r4stl1n/micro-hal/parts/3d-prints/stl/templates/Rear_Cover (Template).stl

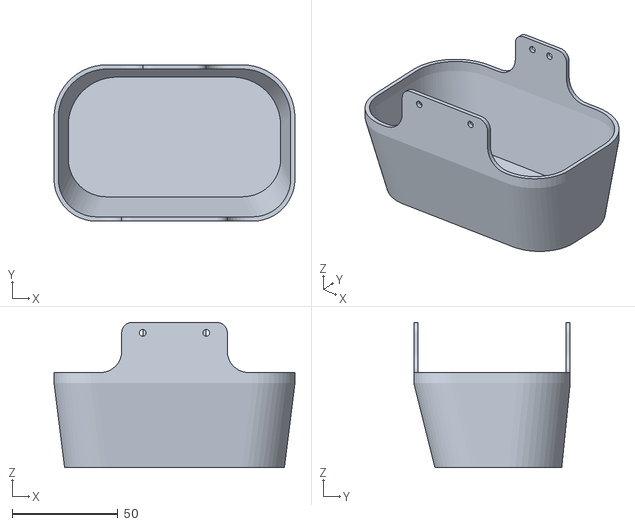
[picture p16: CAD file, 2022-02-13]
parts/3d-prints/stl/templates/Rear_Cover (Template).stl
114.0 x 74.0 x 68.8
