r4stl1n/micro-hal/sim/meshes/stl/ledholder.stl

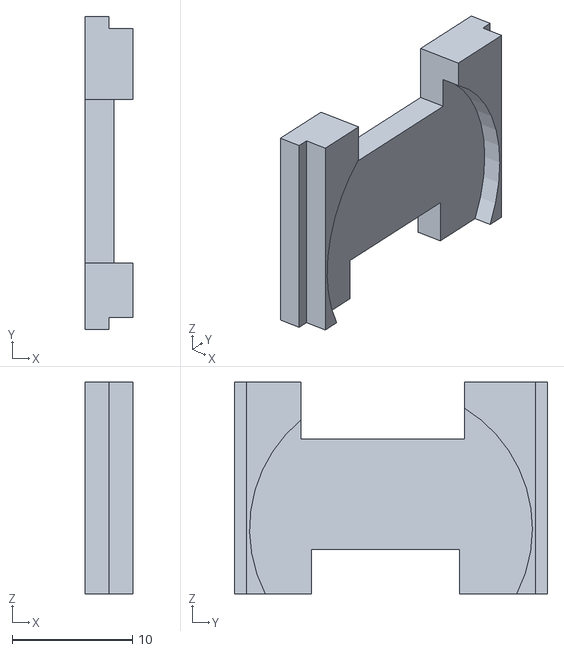
[picture p17: CAD file, 2022-02-22]
sim/meshes/stl/ledholder.stl
4.00 x 26.0 x 17.6
