r4stl1n/micro-hal/parts/3d-prints/freecad/LiPo_Mountingbracket_Front.FCStd

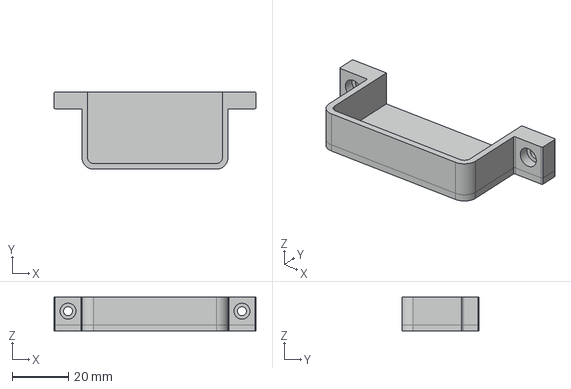
[picture p18: CAD file, 2022-02-13]
parts/3d-prints/freecad/LiPo_Mountingbracket_Front.FCStd
72.0 x 27.5 x 12.0 mm
