r4stl1n/micro-hal/sim/meshes/stl/lshoulder.stl

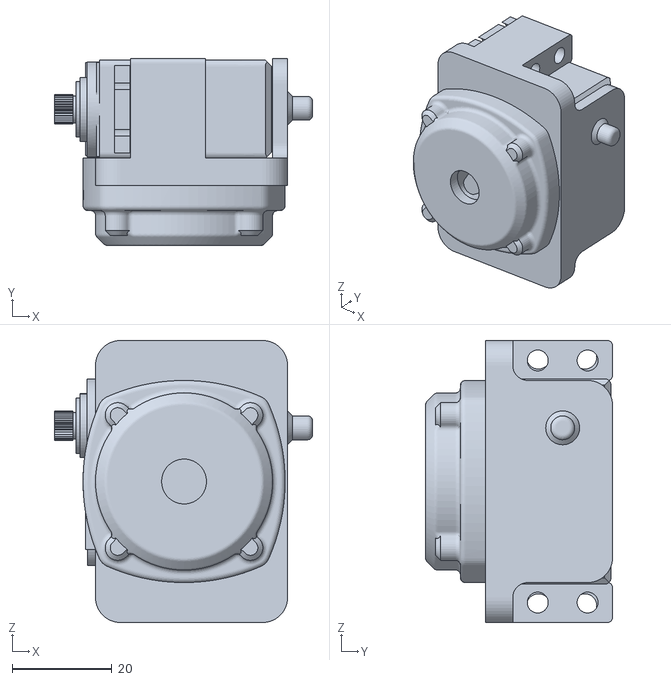
[picture p19: CAD file, 2022-02-22]
sim/meshes/stl/lshoulder.stl
51.7 x 37.5 x 56.5
