r4stl1n/micro-hal/parts/3d-prints/freecad/LiPo_Mountingbracket_Rear.FCStd

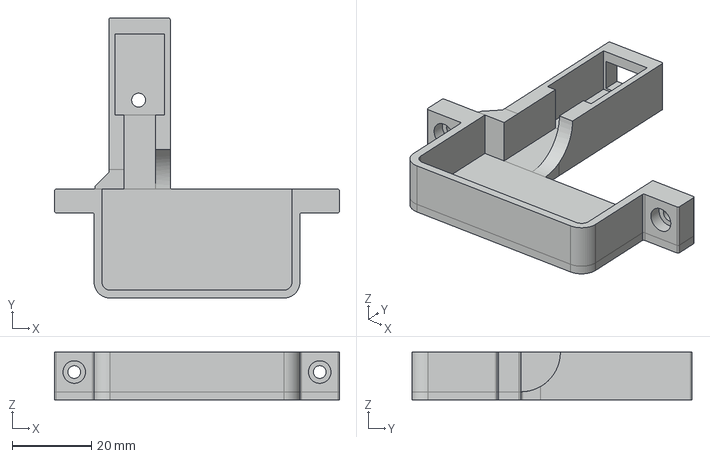
[picture p20: CAD file, 2022-02-13]
parts/3d-prints/freecad/LiPo_Mountingbracket_Rear.FCStd
72.0 x 70.8 x 12.0 mm
