r4stl1n/micro-hal/sim/meshes/stl/backpart.stl

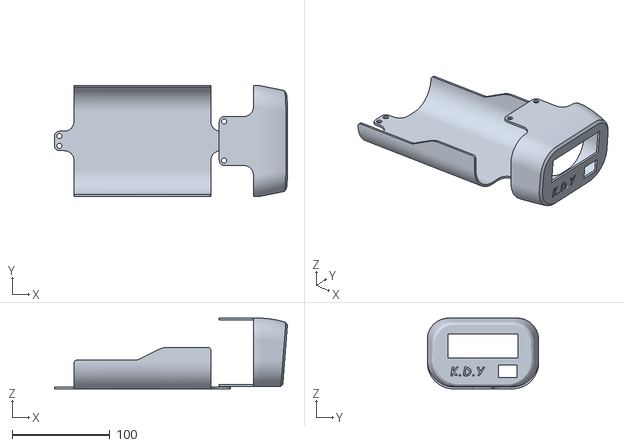
[picture p21: CAD file, 2022-02-22]
sim/meshes/stl/backpart.stl
238.4 x 114.1 x 72.5
