r4stl1n/micro-hal/sim/meshes/stl/F_shoulder.stl

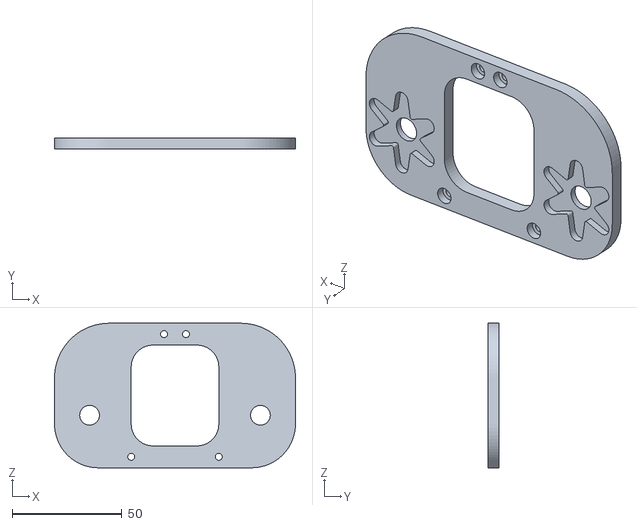
[picture p22: CAD file, 2022-02-22]
sim/meshes/stl/F_shoulder.stl
110.0 x 5.00 x 66.0
