r4stl1n/micro-hal/sim/meshes/stl/foot.stl

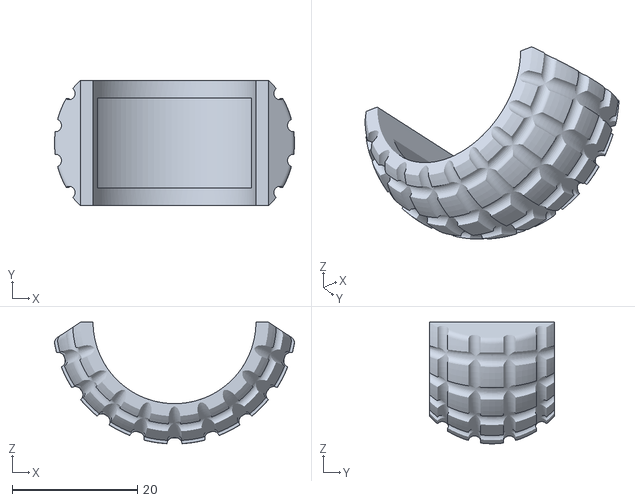
[picture p23: CAD file, 2022-02-22]
sim/meshes/stl/foot.stl
38.3 x 20.0 x 19.4
