r4stl1n/micro-hal/parts/3d-prints/freecad/Shoulder_Joint_Servohorn_Cap.FCStd

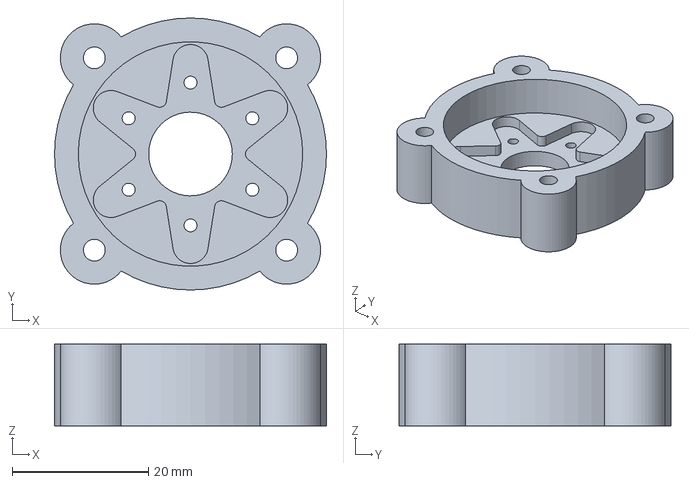
[picture p24: CAD file, 2022-02-13]
parts/3d-prints/freecad/Shoulder_Joint_Servohorn_Cap.FCStd
40.0 x 40.0 x 12.0 mm
