r4stl1n/micro-hal/sim/meshes/stl/non-mega_T_cover.stl

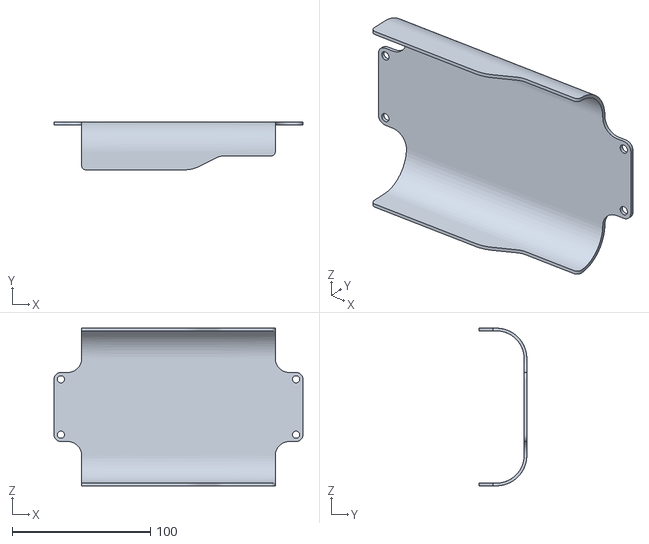
[picture p25: CAD file, 2022-02-22]
sim/meshes/stl/non-mega_T_cover.stl
180.0 x 34.5 x 114.0
