r4stl1n/micro-hal/sim/meshes/stl/batteryholder.stl

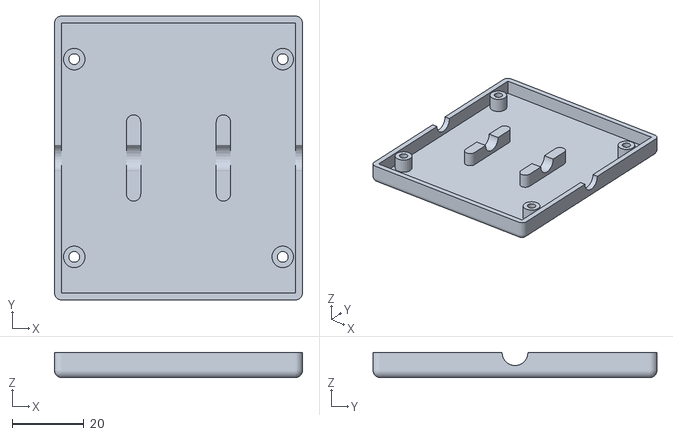
[picture p26: CAD file, 2022-02-22]
sim/meshes/stl/batteryholder.stl
69.0 x 79.0 x 7.00
