r4stl1n/micro-hal/parts/3d-prints/freecad/LiPo_Mountingbracket_Middle.FCStd

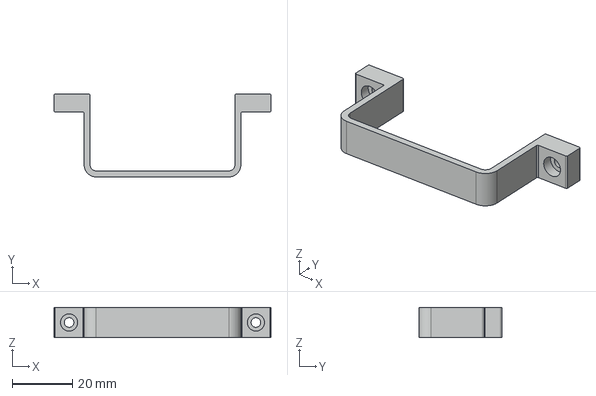
[picture p27: CAD file, 2022-02-13]
parts/3d-prints/freecad/LiPo_Mountingbracket_Middle.FCStd
72.0 x 27.5 x 10.0 mm
