r4stl1n/micro-hal/sim/meshes/stl/jetsonPlate.stl

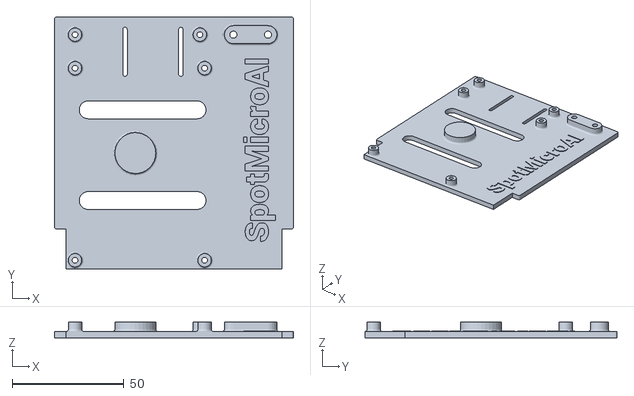
[picture p28: CAD file, 2022-02-22]
sim/meshes/stl/jetsonPlate.stl
107.0 x 113.0 x 7.10
