r4stl1n/micro-hal/parts/3d-prints/freecad/Limb_Top_Shell.FCStd

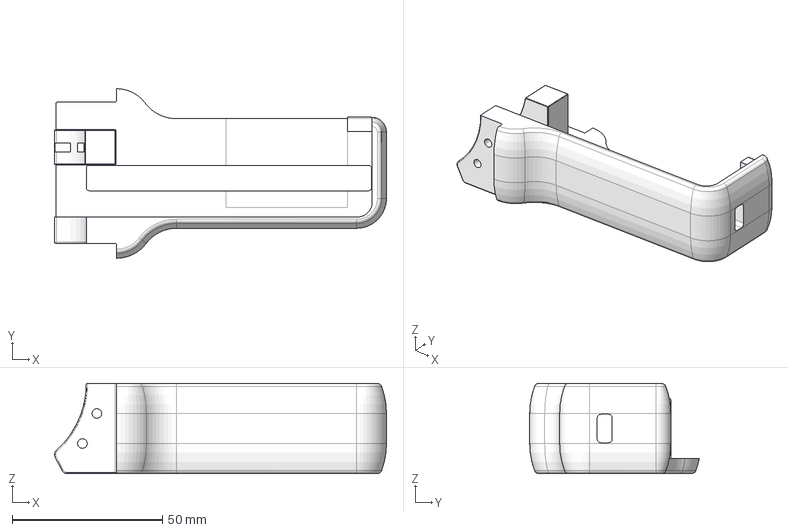
[picture p29: CAD file, 2022-02-13]
parts/3d-prints/freecad/Limb_Top_Shell.FCStd
110.6 x 56.5 x 30.0 mm
