r4stl1n/micro-hal/sim/meshes/stl/R_arm.stl

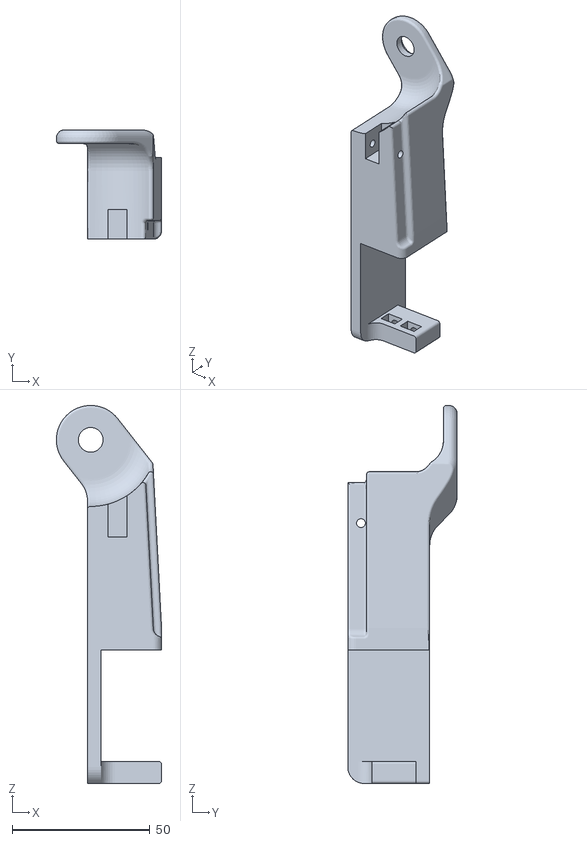
[picture p30: CAD file, 2022-02-22]
sim/meshes/stl/R_arm.stl
38.2 x 39.8 x 137.4
