r4stl1n/micro-hal/parts/3d-prints/freecad/Inner_Shoulder.FCStd

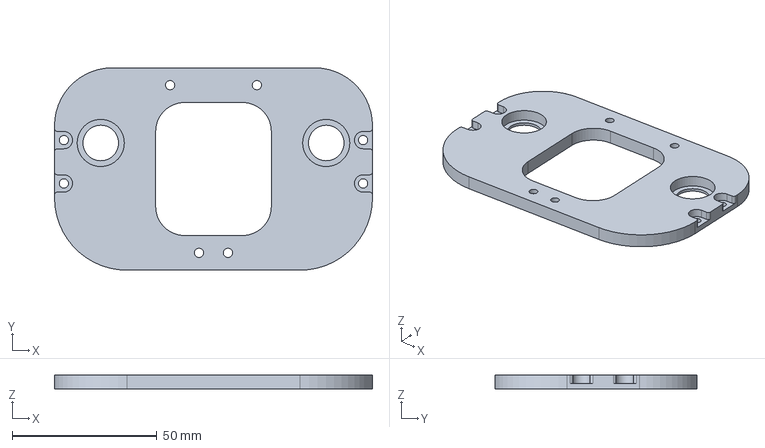
[picture p32: CAD file, 2022-02-13]
parts/3d-prints/freecad/Inner_Shoulder.FCStd
110.0 x 70.0 x 5.00 mm
