r4stl1n/micro-hal/sim/meshes/stl/R_side_plate.stl

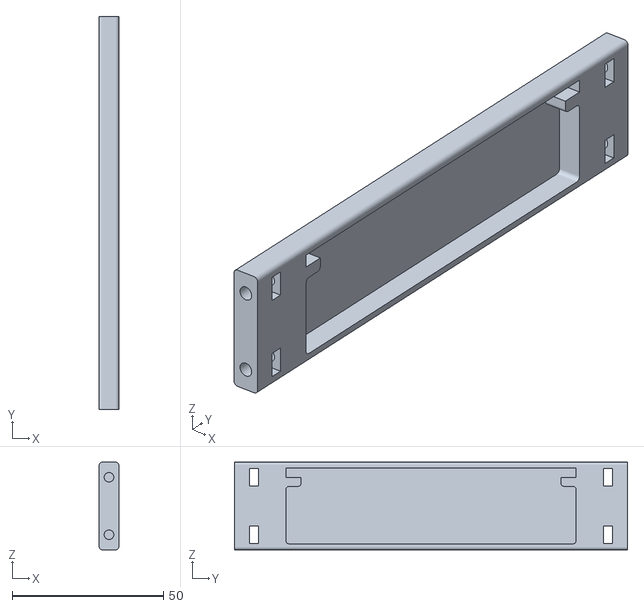
[picture p33: CAD file, 2022-02-22]
sim/meshes/stl/R_side_plate.stl
6.50 x 130.0 x 29.0
