r4stl1n/micro-hal/parts/3d-prints/freecad/Wrist.FCStd

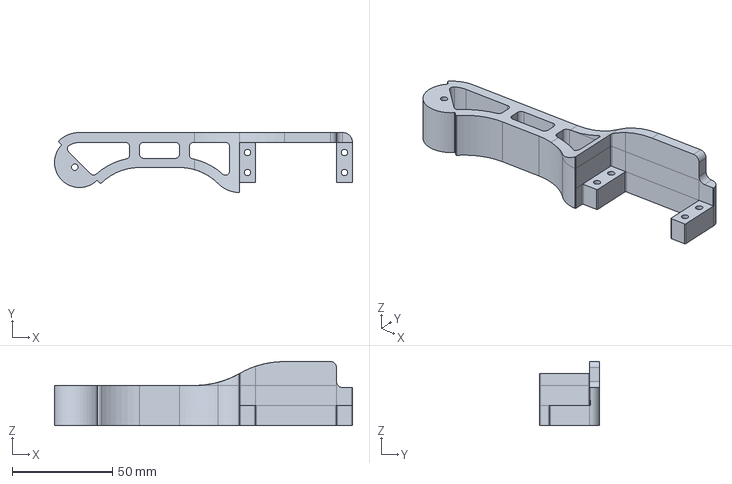
[picture p34: CAD file, 2022-02-13]
parts/3d-prints/freecad/Wrist.FCStd
149.0 x 30.0 x 32.0 mm
