r4stl1n/micro-hal/sim/meshes/stl/lfoot.stl

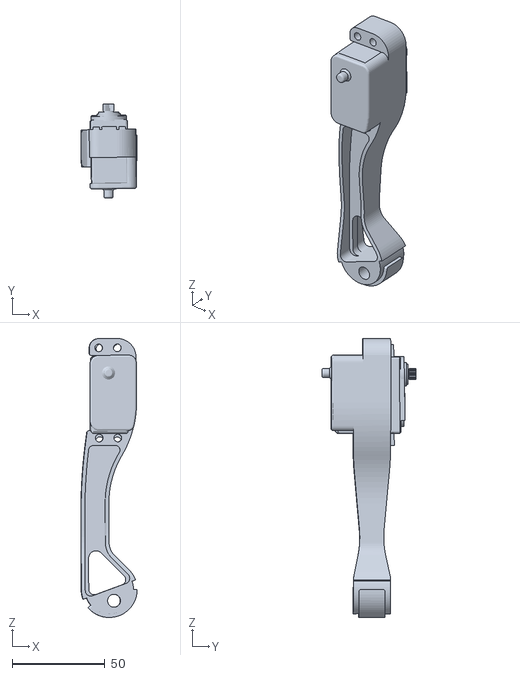
[picture p35: CAD file, 2022-02-22]
sim/meshes/stl/lfoot.stl
30.4 x 50.7 x 150.0
