r4stl1n/micro-hal/parts/3d-prints/freecad/Shoulder_Joint_Ball_Bearing_Pin.FCStd

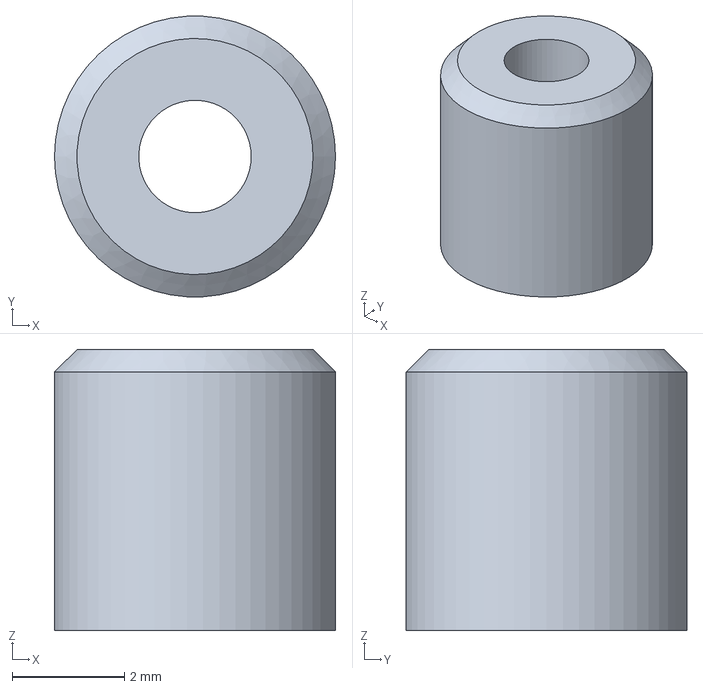
[picture p36: CAD file, 2022-02-13]
parts/3d-prints/freecad/Shoulder_Joint_Ball_Bearing_Pin.FCStd
5.00 x 4.99 x 5.00 mm
