r4stl1n/micro-hal/parts/3d-prints/freecad/Bottom_Cover_Split_Rear.FCStd

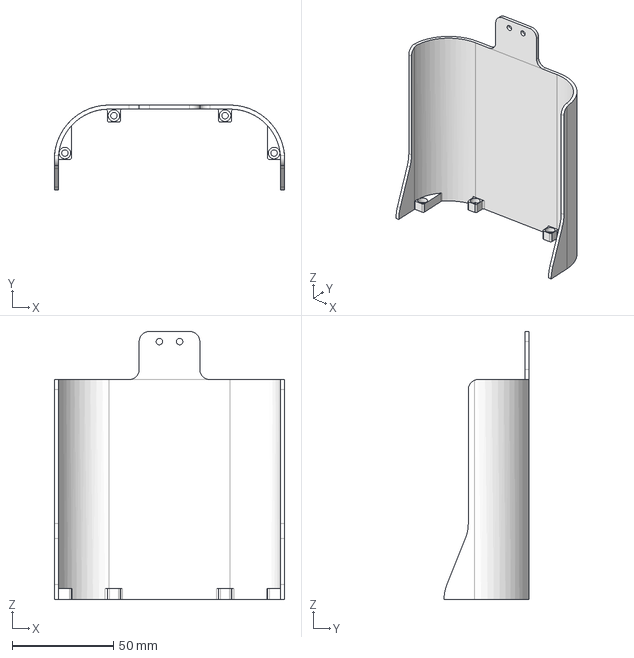
[picture p37: CAD file, 2022-02-13]
parts/3d-prints/freecad/Bottom_Cover_Split_Rear.FCStd
114.0 x 42.0 x 132.6 mm
