r4stl1n/micro-hal/sim/meshes/stl/rear.stl

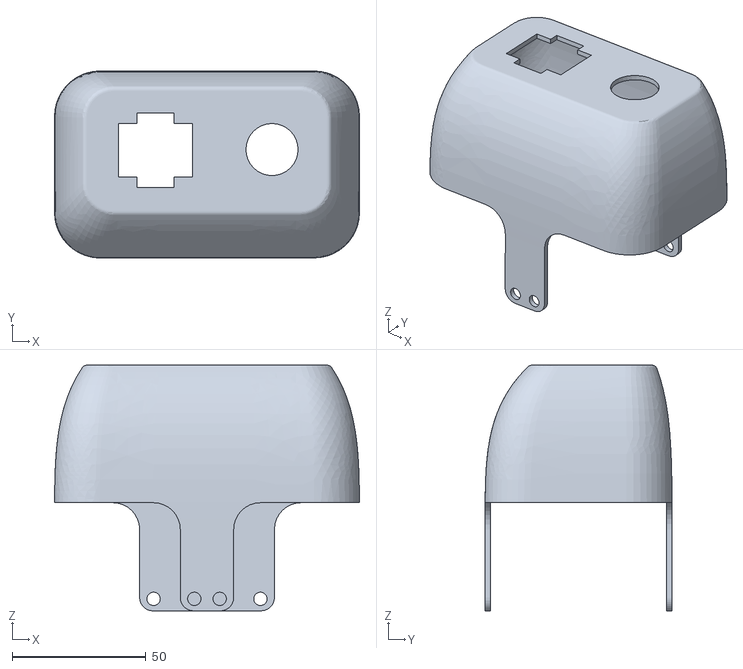
[picture p38: CAD file, 2022-02-22]
sim/meshes/stl/rear.stl
114.2 x 70.0 x 92.0
