r4stl1n/micro-hal/parts/3d-prints/freecad/Limb_Servohorn_Mount_long_v4.FCStd

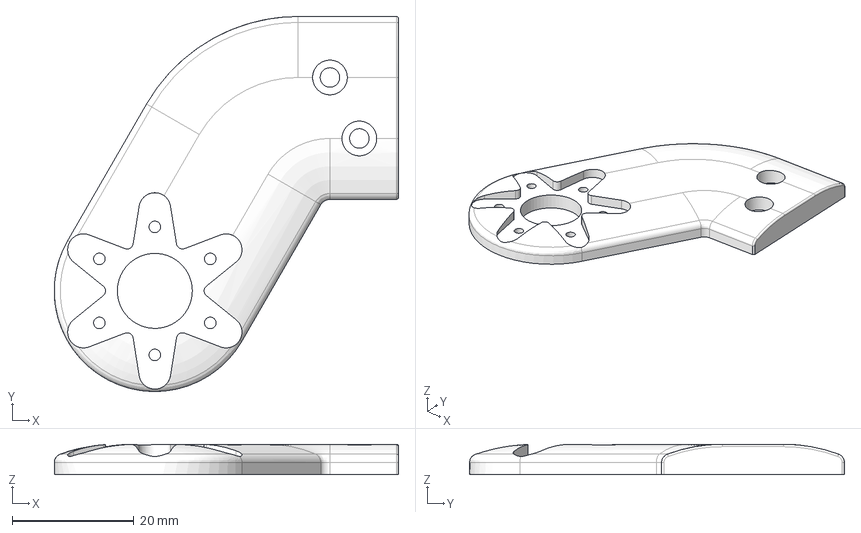
[picture p39: CAD file, 2022-02-13]
parts/3d-prints/freecad/Limb_Servohorn_Mount_long_v4.FCStd
56.5 x 61.5 x 5.00 mm
