r4stl1n/micro-hal/sim/meshes/stl/L_arm_joint.stl

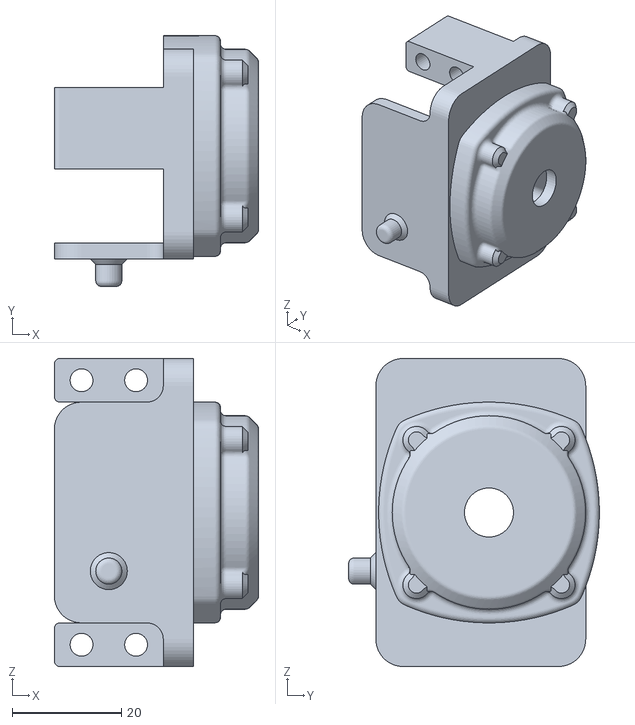
[picture p40: CAD file, 2022-02-22]
sim/meshes/stl/L_arm_joint.stl
37.5 x 46.0 x 56.5
