r4stl1n/micro-hal/parts/3d-prints/freecad/Chassis_Side.FCStd

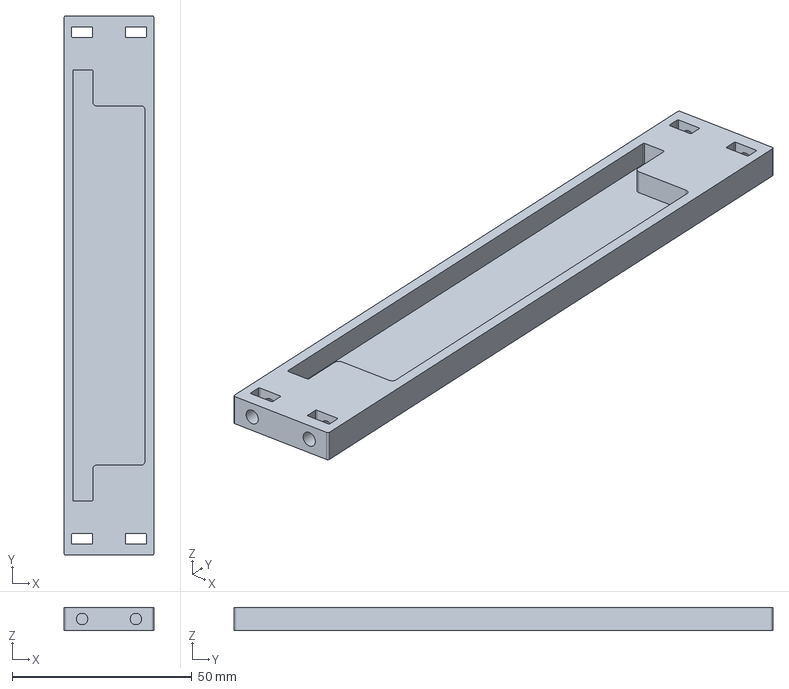
[picture p41: CAD file, 2022-02-13]
parts/3d-prints/freecad/Chassis_Side.FCStd
25.0 x 150.0 x 6.50 mm
