r4stl1n/micro-hal/parts/3d-prints/freecad/TTL_Counterpiece.FCStd

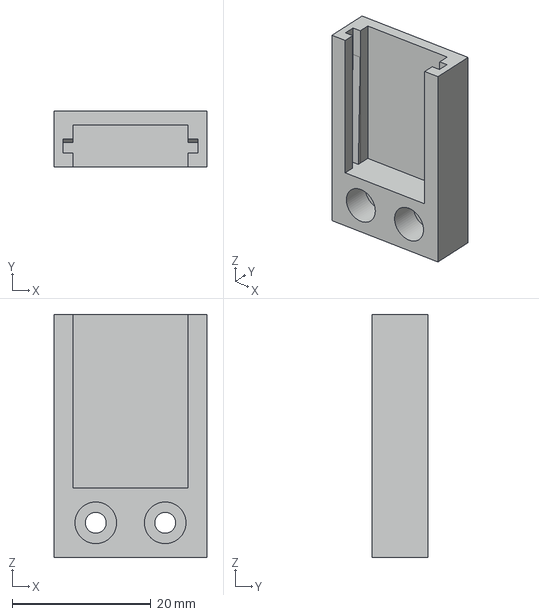
[picture p42: CAD file, 2022-02-13]
parts/3d-prints/freecad/TTL_Counterpiece.FCStd
22.0 x 8.00 x 35.0 mm
