r4stl1n/micro-hal/sim/meshes/stl/plate.stl

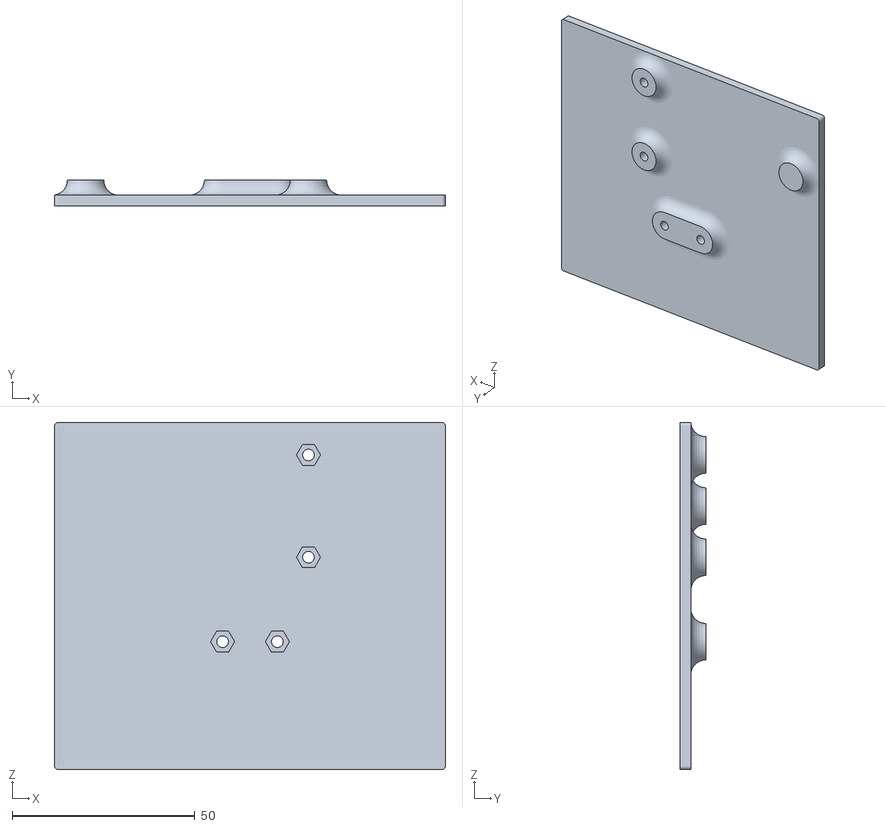
[picture p43: CAD file, 2022-02-22]
sim/meshes/stl/plate.stl
107.0 x 7.00 x 95.0
