r4stl1n/micro-hal/parts/3d-prints/freecad/Bottom_Shoulder.FCStd

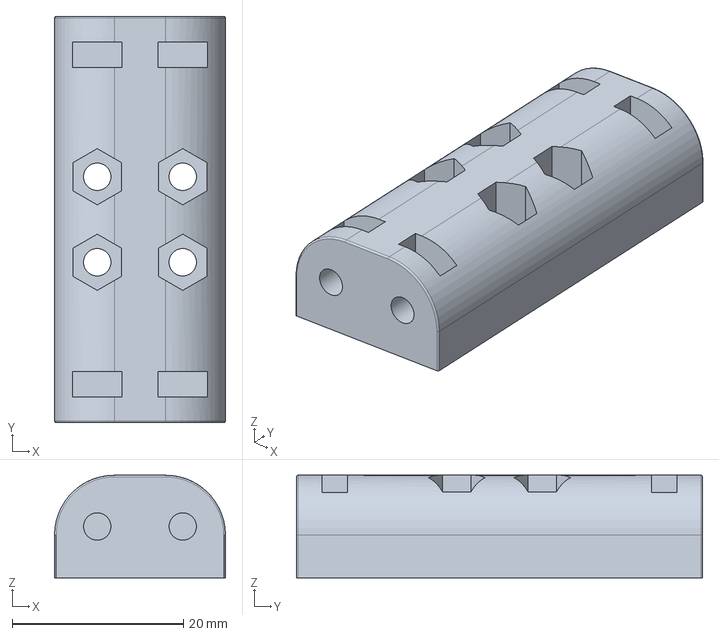
[picture p44: CAD file, 2022-02-13]
parts/3d-prints/freecad/Bottom_Shoulder.FCStd
20.0 x 47.5 x 12.0 mm
