r4stl1n/micro-hal/sim/meshes/stl/frontpart.stl

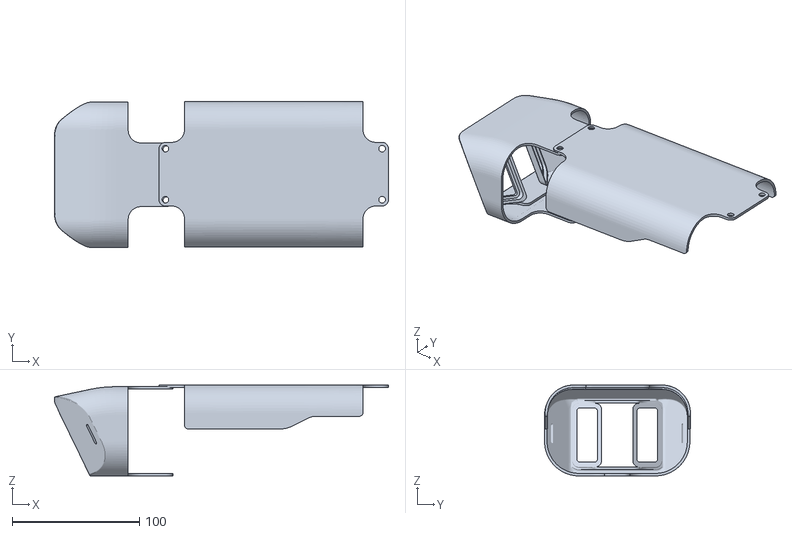
[picture p45: CAD file, 2022-02-22]
sim/meshes/stl/frontpart.stl
262.0 x 114.5 x 71.2
