r4stl1n/micro-hal/parts/3d-prints/freecad/Limb_Servohorn_Mount.FCStd

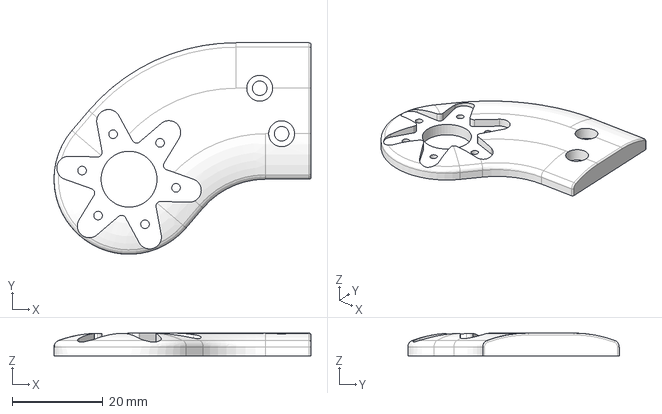
[picture p46: CAD file, 2022-02-13]
parts/3d-prints/freecad/Limb_Servohorn_Mount.FCStd
56.5 x 46.5 x 5.00 mm
