r4stl1n/micro-hal/sim/meshes/stl/F_cover.stl

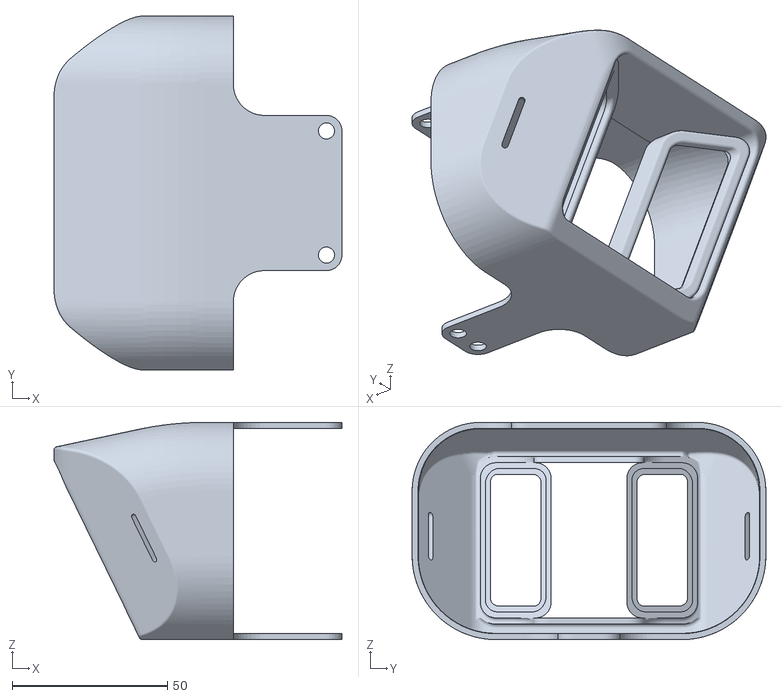
[picture p47: CAD file, 2022-02-22]
sim/meshes/stl/F_cover.stl
92.8 x 114.0 x 70.0
