r4stl1n/micro-hal/parts/3d-prints/freecad/Foot_Tip.FCStd

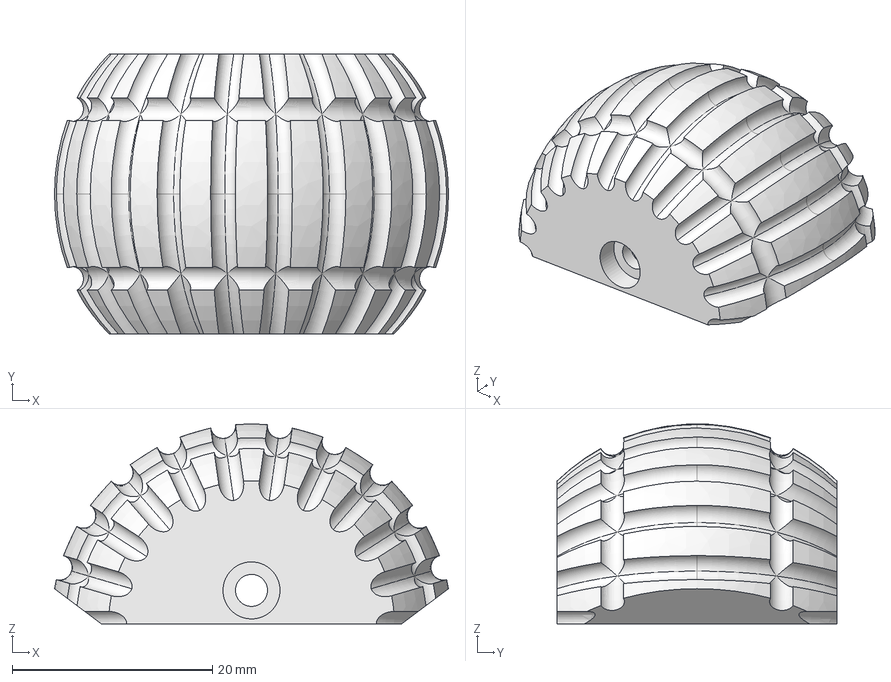
[picture p48: CAD file, 2022-02-13]
parts/3d-prints/freecad/Foot_Tip.FCStd
39.4 x 28.0 x 20.0 mm
