r4stl1n/micro-hal/sim/meshes/stl/label.stl

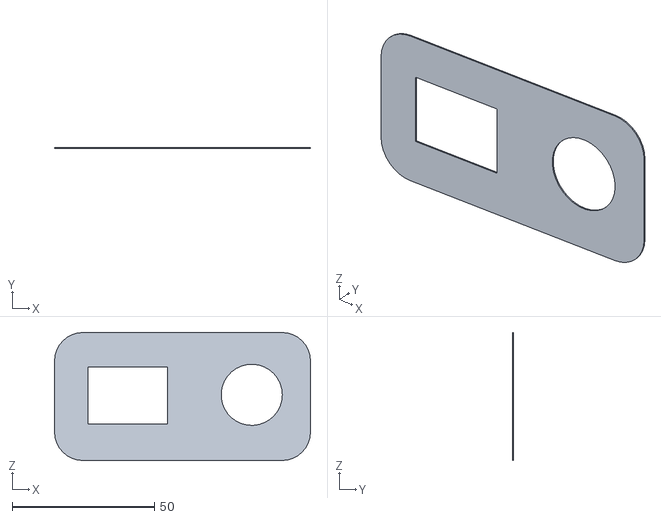
[picture p49: CAD file, 2022-02-22]
sim/meshes/stl/label.stl
90.0 x 0.4 x 45.0
