r4stl1n/micro-hal/parts/3d-prints/freecad/Servohorn_6_B_Star.FCStd

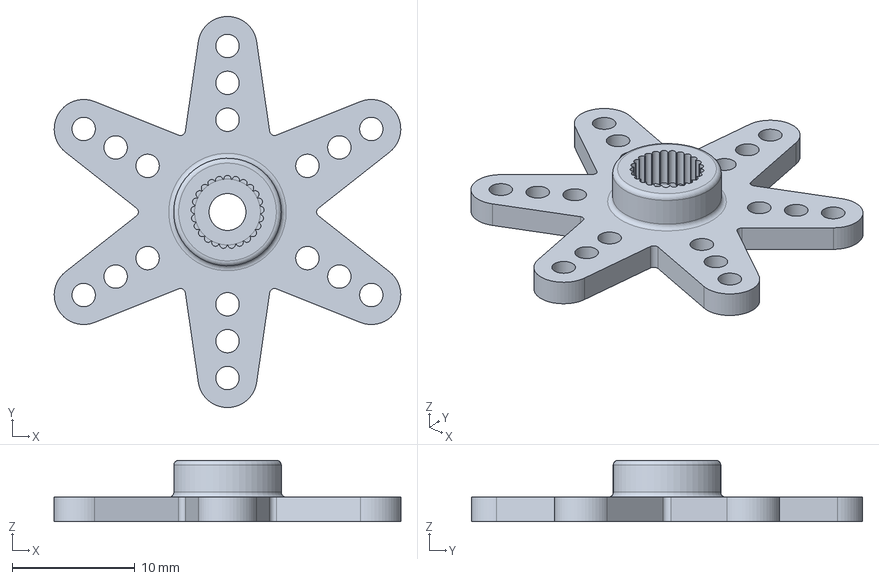
[picture p50: CAD file, 2022-02-13]
parts/3d-prints/freecad/Servohorn_6_B_Star.FCStd
28.2 x 31.8 x 5.00 mm
