r4stl1n/micro-hal/sim/meshes/stl/L_wrist.stl

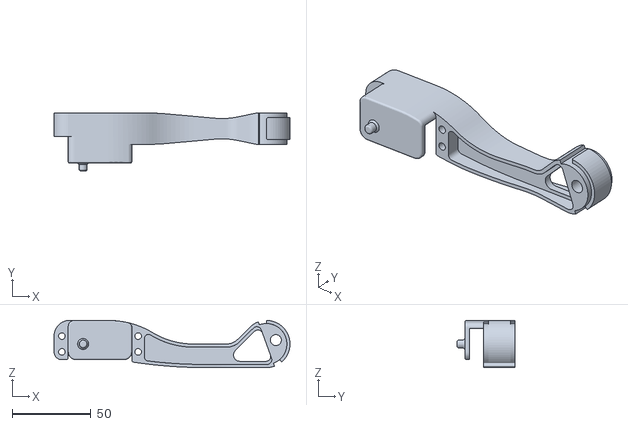
[picture p51: CAD file, 2022-02-22]
sim/meshes/stl/L_wrist.stl
150.0 x 36.9 x 30.0
