r4stl1n/micro-hal/parts/3d-prints/freecad/Rear_Cover_1_77_tft_without_SD.FCStd

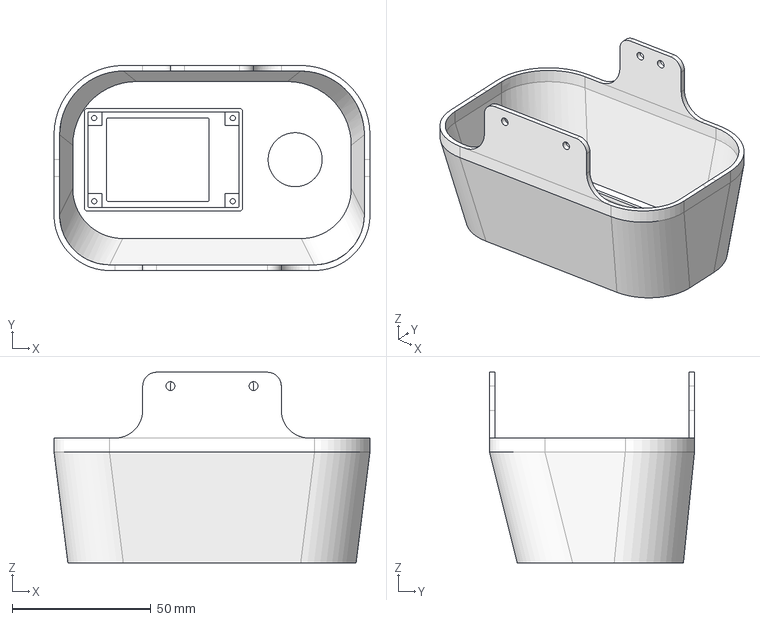
[picture p52: CAD file, 2022-02-13]
parts/3d-prints/freecad/Rear_Cover_1_77_tft_without_SD.FCStd
114.0 x 74.0 x 68.8 mm
