r4stl1n/micro-hal/parts/3d-prints/freecad/Circuitry_Mountingplate_Extended.FCStd

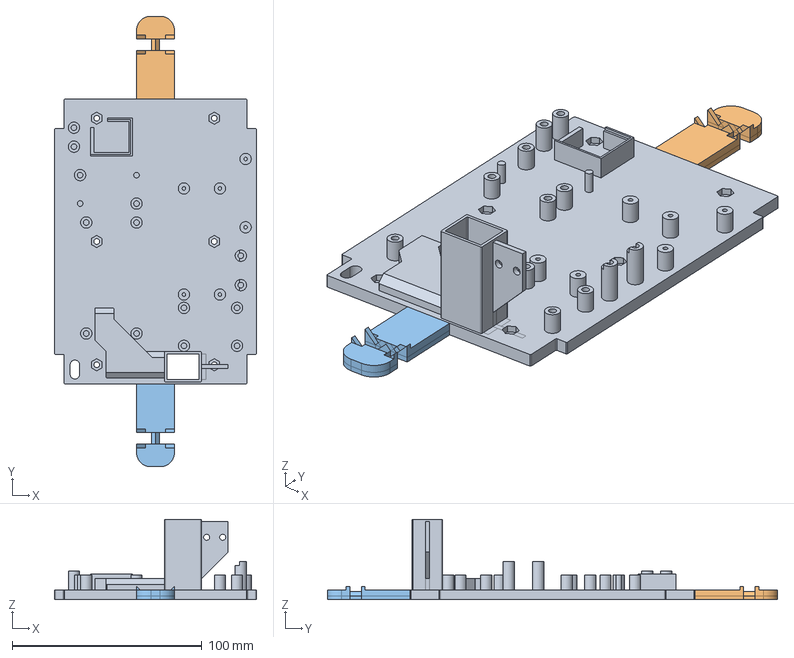
[picture p53: CAD file, 2022-02-13]
parts/3d-prints/freecad/Circuitry_Mountingplate_Extended.FCStd
106.5 x 237.5 x 42.2 mm
Circuitry Mountingplate Base
Circuitry Mountingplate Front Extension
Circuitry Mountingplate Rear Extension
