r4stl1n/micro-hal/parts/3d-prints/freecad/Circuitry_Mountingplate_SZBK07.FCStd

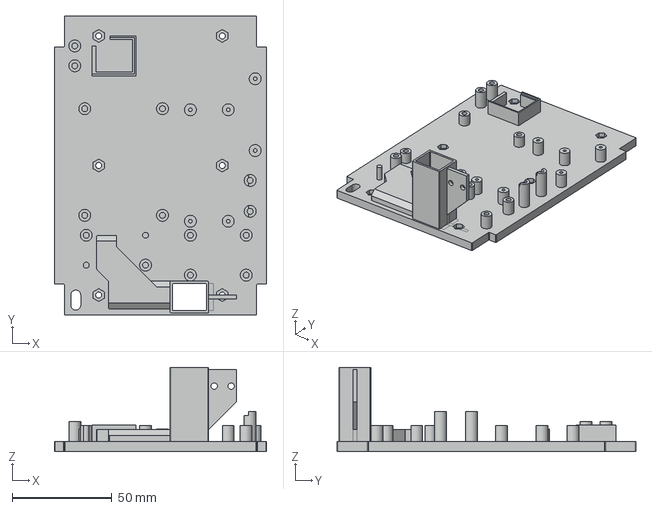
[picture p54: CAD file, 2022-02-13]
parts/3d-prints/freecad/Circuitry_Mountingplate_SZBK07.FCStd
106.5 x 150.0 x 42.2 mm
