r4stl1n/micro-hal/sim/meshes/stl/non-mega_B_cover.stl

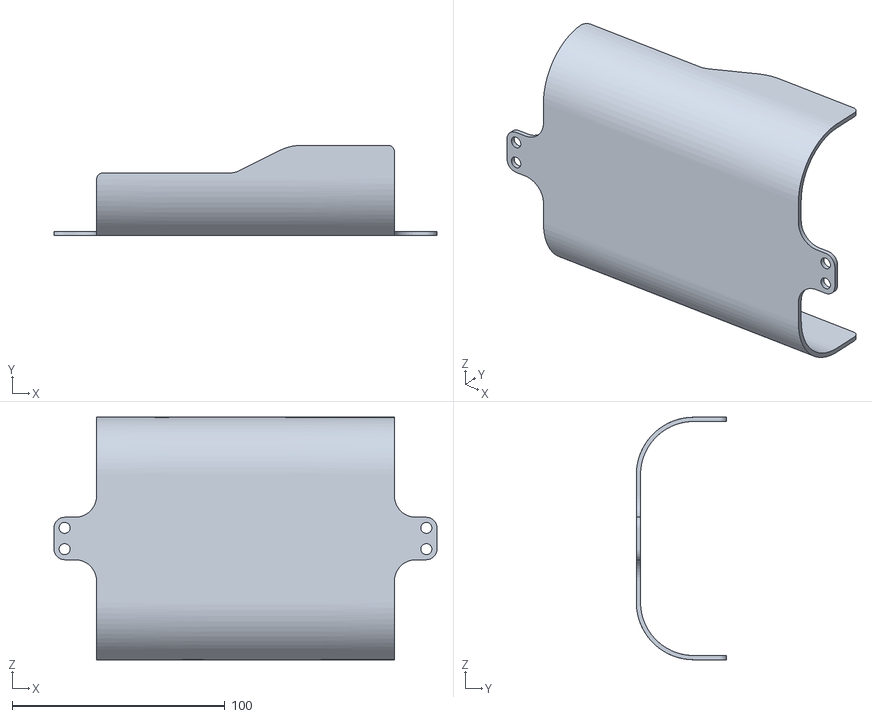
[picture p55: CAD file, 2022-02-22]
sim/meshes/stl/non-mega_B_cover.stl
180.0 x 42.5 x 114.0
