r4stl1n/micro-hal/parts/3d-prints/freecad/Rear_Cover_long_1_8_tft_with_SD.FCStd

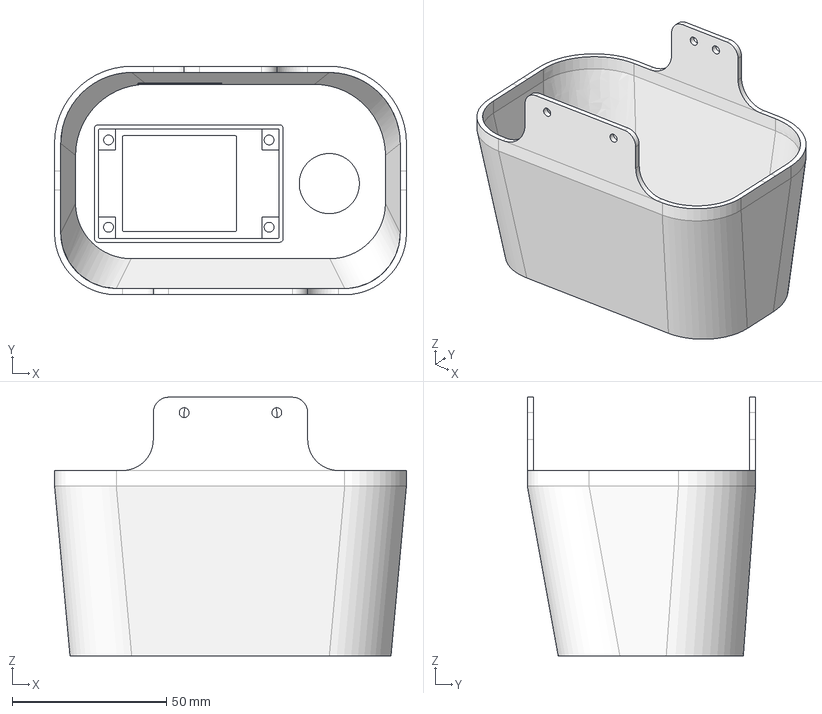
[picture p56: CAD file, 2022-02-13]
parts/3d-prints/freecad/Rear_Cover_long_1_8_tft_with_SD.FCStd
114.0 x 74.0 x 83.7 mm
