r4stl1n/micro-hal/parts/3d-prints/freecad/cameramount_esp32_cam.FCStd

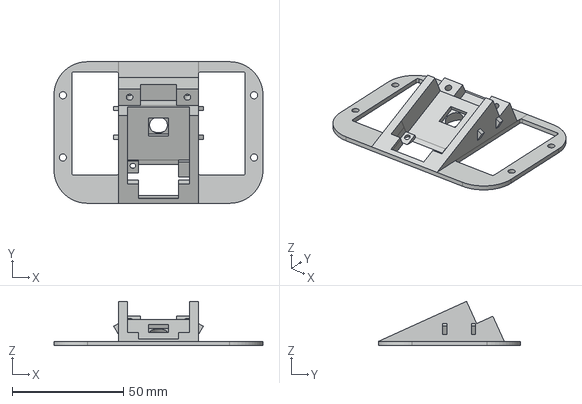
[picture p58: CAD file, 2022-02-13]
parts/3d-prints/freecad/cameramount_esp32_cam.FCStd
94.0 x 63.7 x 20.0 mm
