r4stl1n/micro-hal/parts/3d-prints/freecad/Limb_Bottom_Shell.FCStd

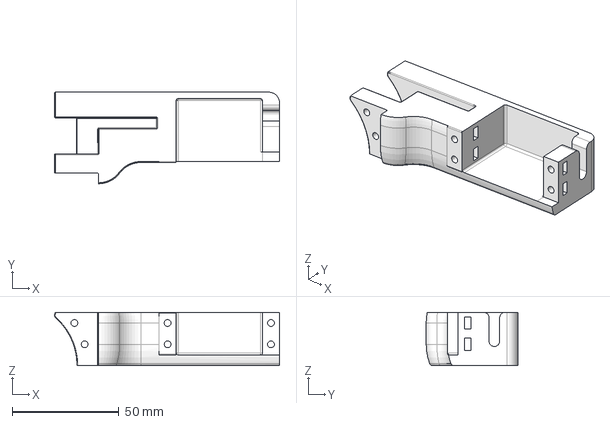
[picture p59: CAD file, 2022-02-13]
parts/3d-prints/freecad/Limb_Bottom_Shell.FCStd
105.6 x 43.0 x 25.0 mm
