r4stl1n/micro-hal/parts/3d-prints/freecad/Top_Cover_Split_Rear.FCStd

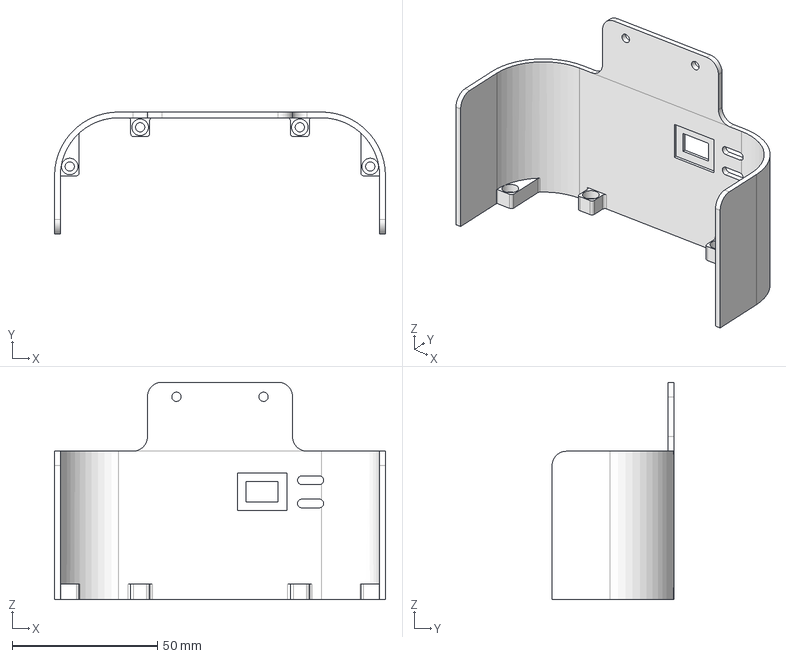
[picture p60: CAD file, 2022-02-13]
parts/3d-prints/freecad/Top_Cover_Split_Rear.FCStd
114.0 x 42.0 x 74.9 mm
