r4stl1n/micro-hal/sim/meshes/stl/top.stl

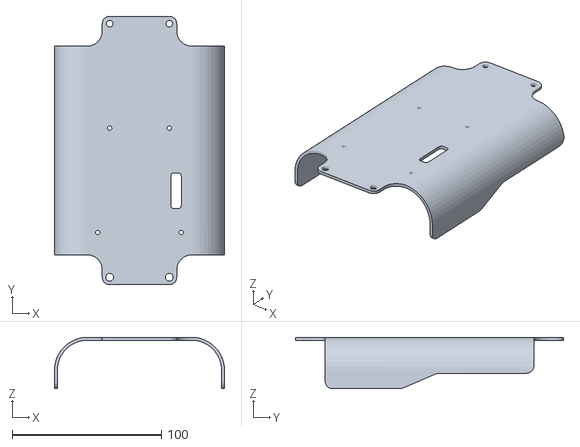
[picture p61: CAD file, 2022-02-22]
sim/meshes/stl/top.stl
114.0 x 180.0 x 34.5
