r4stl1n/micro-hal/parts/3d-prints/freecad/Wrist _Counterpart.FCStd

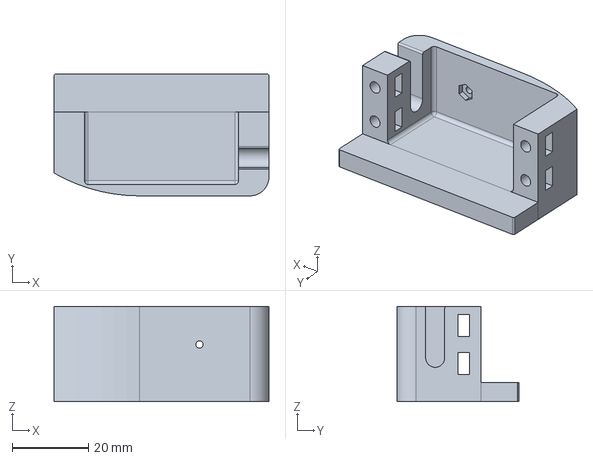
[picture p62: CAD file, 2022-02-13]
parts/3d-prints/freecad/Wrist _Counterpart.FCStd
56.5 x 32.0 x 25.0 mm
