r4stl1n/micro-hal/parts/3d-prints/freecad/Rear_Cover_Plate.FCStd

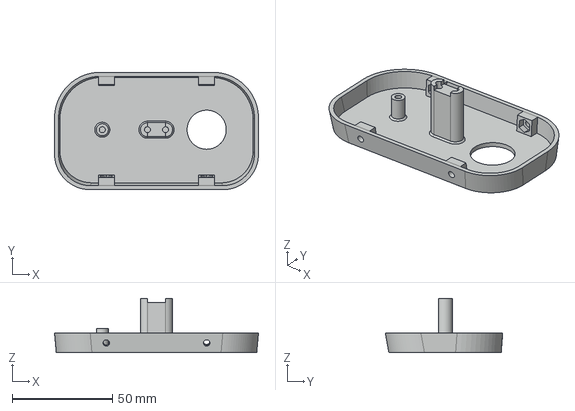
[picture p64: CAD file, 2022-02-13]
parts/3d-prints/freecad/Rear_Cover_Plate.FCStd
101.7 x 58.5 x 27.0 mm
