r4stl1n/micro-hal/sim/meshes/stl/bottom.stl

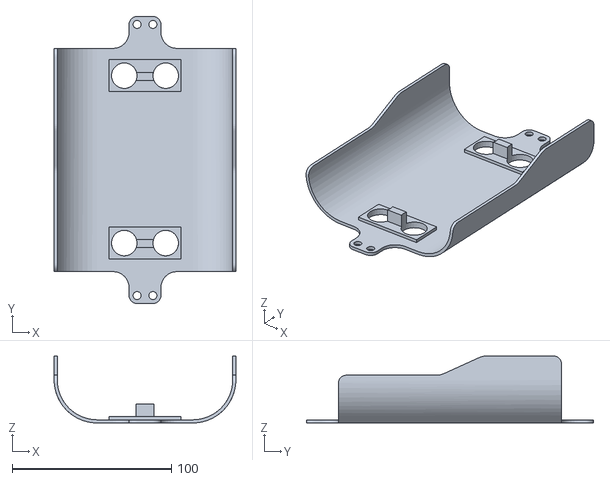
[picture p65: CAD file, 2022-02-22]
sim/meshes/stl/bottom.stl
114.0 x 180.0 x 42.0
