r4stl1n/micro-hal/sim/meshes/stl/R_cover.stl

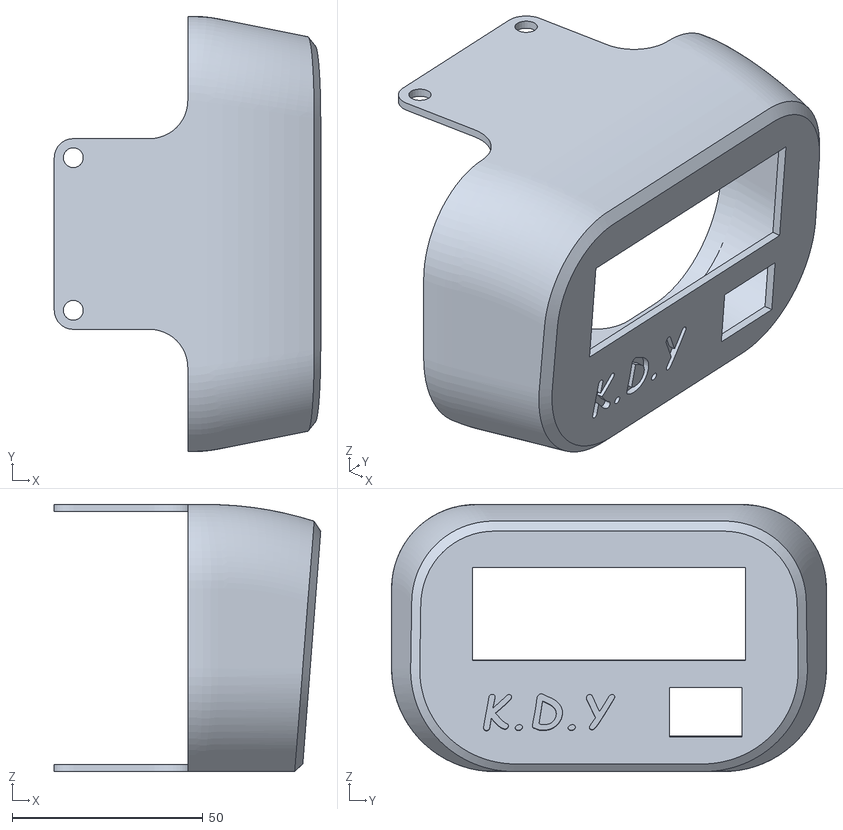
[picture p66: CAD file, 2022-02-22]
sim/meshes/stl/R_cover.stl
69.8 x 114.0 x 70.0
