r4stl1n/micro-hal/parts/3d-prints/freecad/cameramount_esp32_cam_counterpiece.FCStd

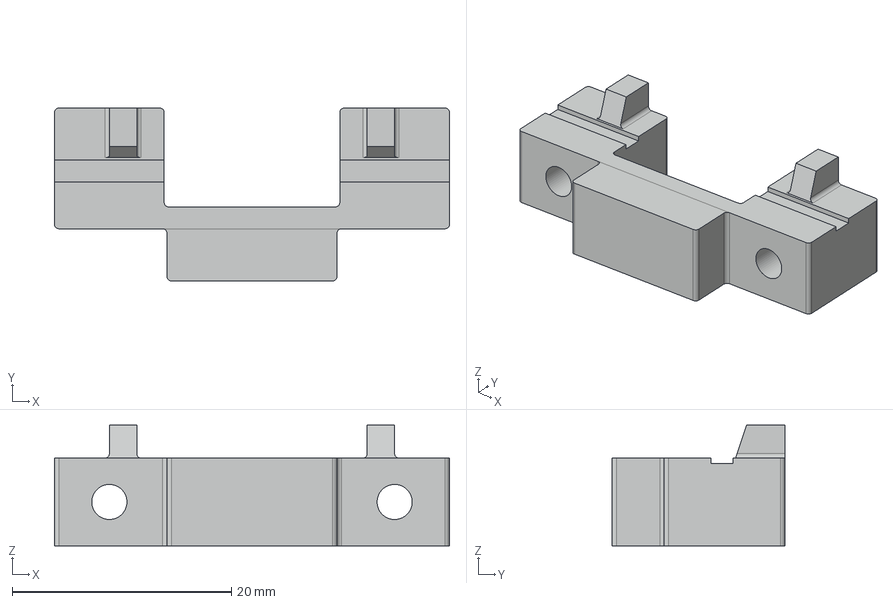
[picture p67: CAD file, 2022-02-13]
parts/3d-prints/freecad/cameramount_esp32_cam_counterpiece.FCStd
36.0 x 15.8 x 11.0 mm
