r4stl1n/micro-hal/parts/3d-prints/freecad/Shoulder_Joint_Servomount.FCStd

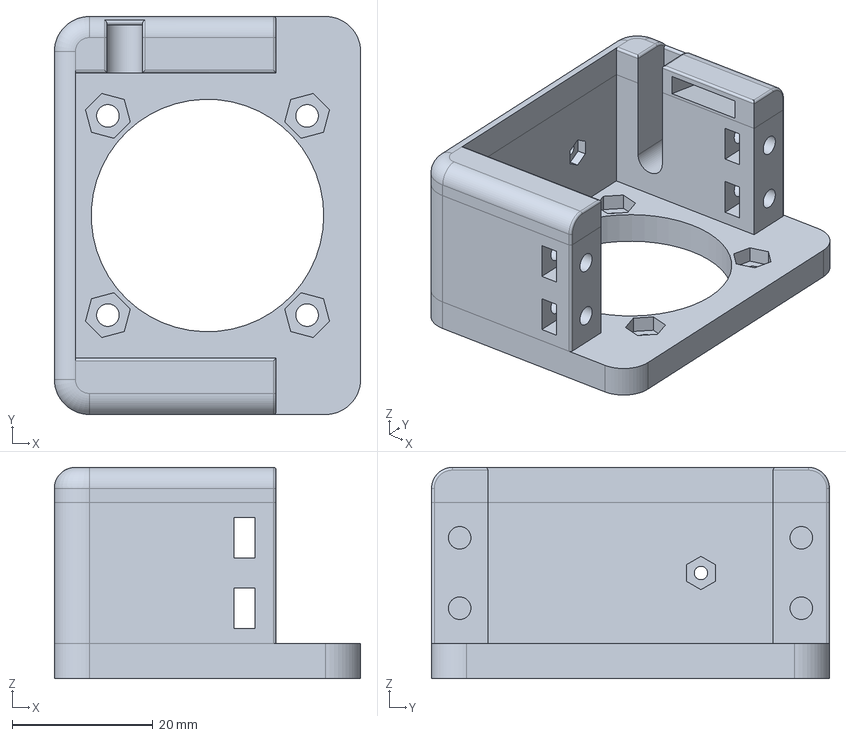
[picture p68: CAD file, 2022-02-13]
parts/3d-prints/freecad/Shoulder_Joint_Servomount.FCStd
43.5 x 56.5 x 30.0 mm
