r4stl1n/micro-hal/parts/3d-prints/freecad/Front_Cover_Optimized.FCStd

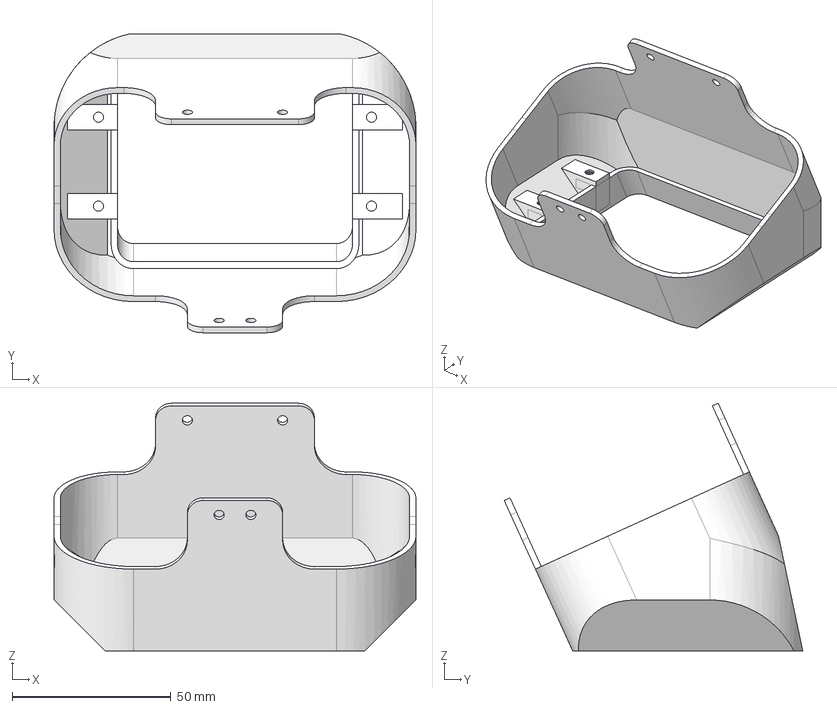
[picture p69: CAD file, 2022-02-13]
parts/3d-prints/freecad/Front_Cover_Optimized.FCStd
114.0 x 94.0 x 78.0 mm
