r4stl1n/micro-hal/sim/meshes/stl/batteryholder2.stl

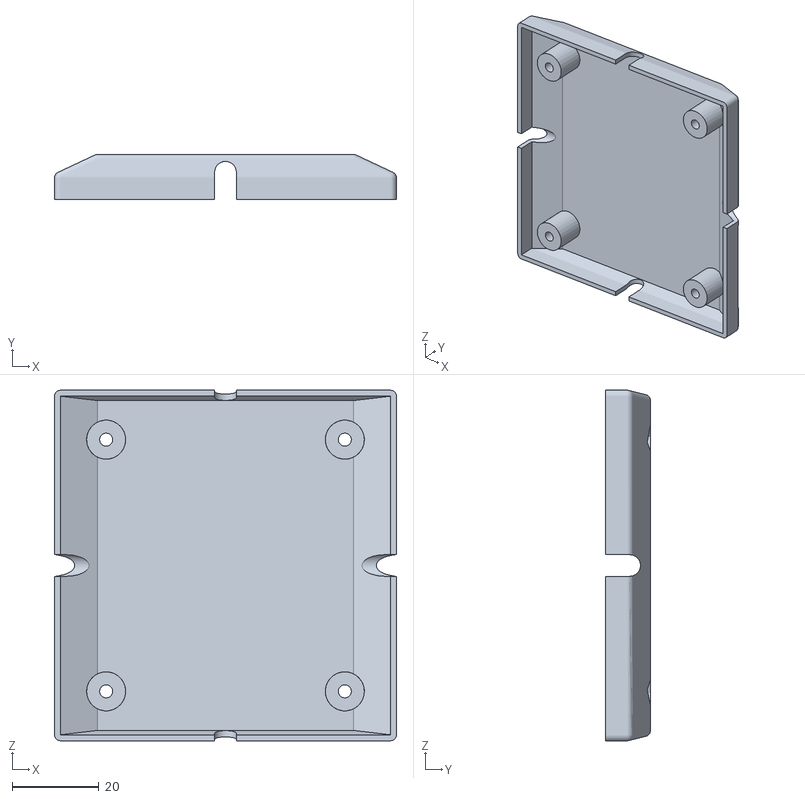
[picture p70: CAD file, 2022-02-22]
sim/meshes/stl/batteryholder2.stl
78.8 x 10.4 x 80.8
