r4stl1n/micro-hal/sim/meshes/stl/R_shoulder.stl

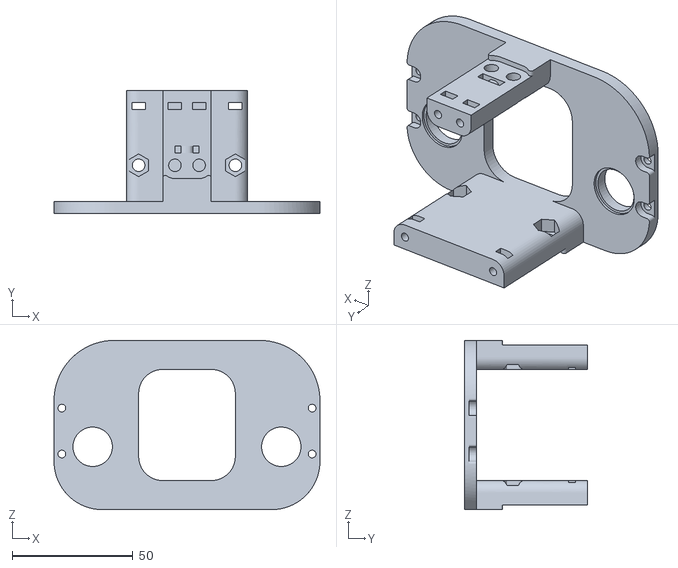
[picture p71: CAD file, 2022-02-22]
sim/meshes/stl/R_shoulder.stl
110.0 x 51.0 x 70.0
