r4stl1n/micro-hal/parts/3d-prints/freecad/Bottom_Cover_Split_Front.FCStd

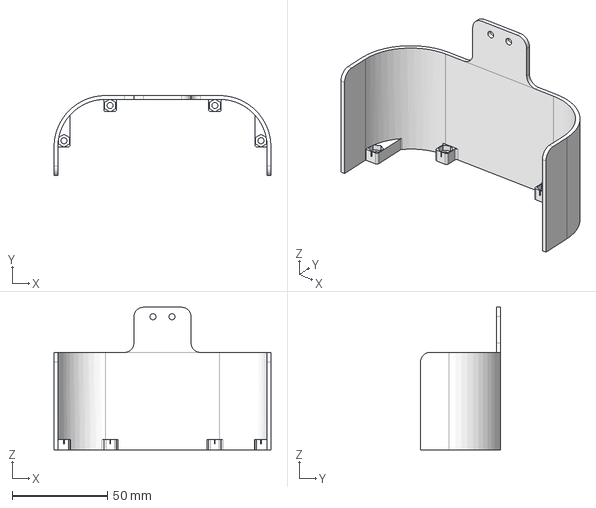
[picture p72: CAD file, 2022-02-13]
parts/3d-prints/freecad/Bottom_Cover_Split_Front.FCStd
114.0 x 42.0 x 74.9 mm
