r4stl1n/micro-hal/parts/3d-prints/freecad/Top_Shoulder.FCStd

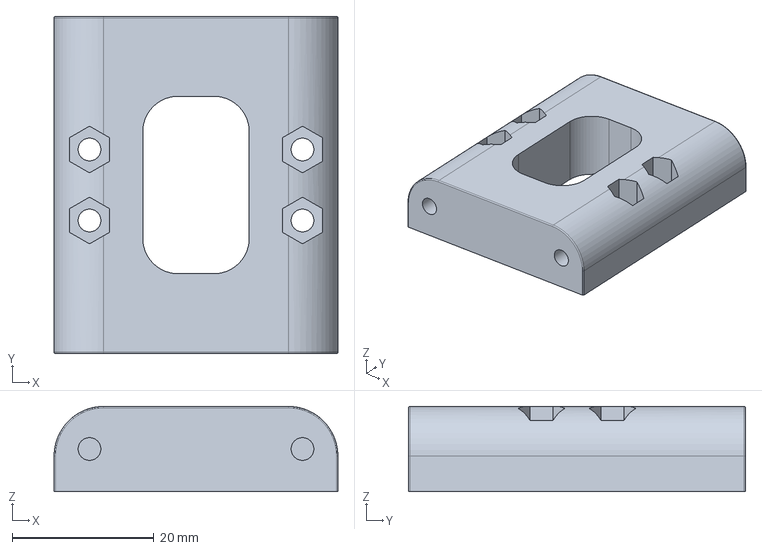
[picture p74: CAD file, 2022-02-13]
parts/3d-prints/freecad/Top_Shoulder.FCStd
40.0 x 47.5 x 12.0 mm
