r4stl1n/micro-hal/parts/3d-prints/freecad/Cameramount.FCStd

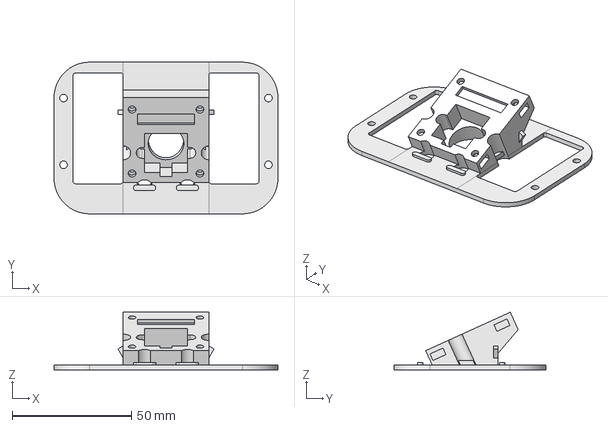
[picture p75: CAD file, 2022-02-13]
parts/3d-prints/freecad/Cameramount.FCStd
94.0 x 63.7 x 24.2 mm
